peterjose/WeCare-iBoard/src/WeCare_iBoard/Sensor.hpp

/**
 * @file Sensor.hpp
 * @author Team Hugo
 * @brief Provide functionalities for updating with the sensor inputs
 * @version 0.1
 * @date 2020-12-27
 * 
 * @copyright Copyright (c) 2020
 * 
 */

#ifndef _SENSOR_H_
#define _SENSOR_H_

void updateSensorStatus(void);


#endif /* _SENSOR_H_ */
