peterjose/WeCare-iBoard/src/WeCare_iBoard_ESP_NetworkAdaptor/MQTT_Connector.hpp

/**
 * @file MQTT_Connector.hpp
 * @author Team Hugo
 * @brief 
 * @version 0.1
 * @date 2021-01-30
 * 
 * @copyright Copyright (c) 2021
 * 
 */

#ifndef _MQTT_CONNECTOR_H_
#define _MQTT_CONNECTOR_H_

void Initialise_MQTT(void);
void MQTT_TaskRunner(void);

#endif /* _MQTT_CONNECTOR_H_ */
