peterjose/WeCare-iBoard/src/WeCare_iBoard/NetworkCommunicationModule.hpp

/**
 * @file NetworkCommunicationModule.hpp
 * @author Team Hugo
 * @brief File provides necessary functions for the connection of two boards
 * @version 0.1
 * @date 2020-12-27
 * 
 * @copyright Copyright (c) 2020
 * 
 */

#ifndef _NETWORK_COMMUNICATION_MODULE_H_
#define _NETWORK_COMMUNICATION_MODULE_H_

void EstablishedInterBoardConnection(int pixelCount);
void ConnectionTaskRunner(CubeModule_t interactiveBoard[], int pixelCount);

#endif /* _NETWORK_COMMUNICATION_MODULE_H_ */
